dimajolkin/sms-telegram/docs/hardware/enclosure-bottom-iso.png

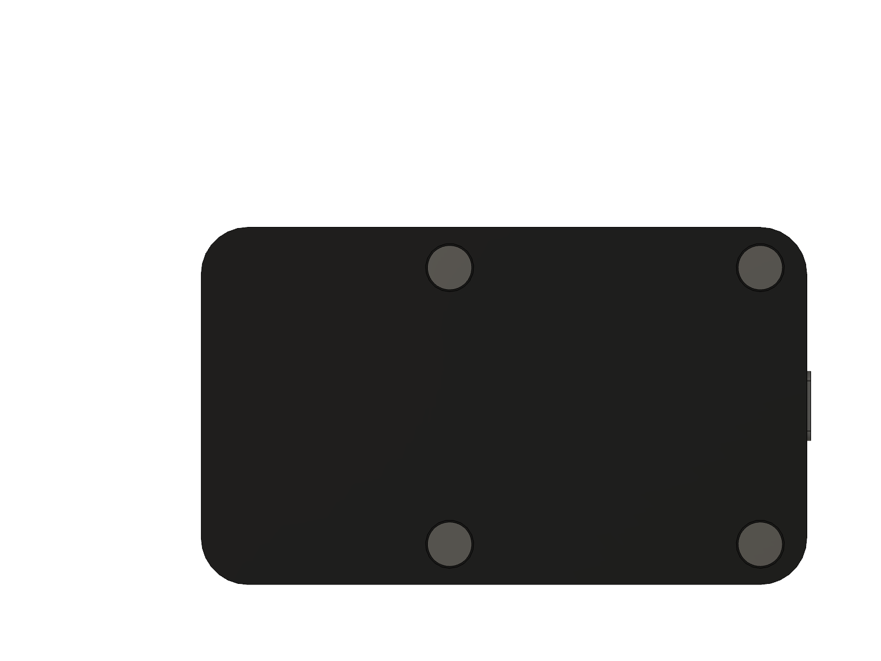
docs/hardware/enclosure-bottom-iso.png
