dimajolkin/sms-telegram/docs/hardware/enclosure-cover-fixtures.png

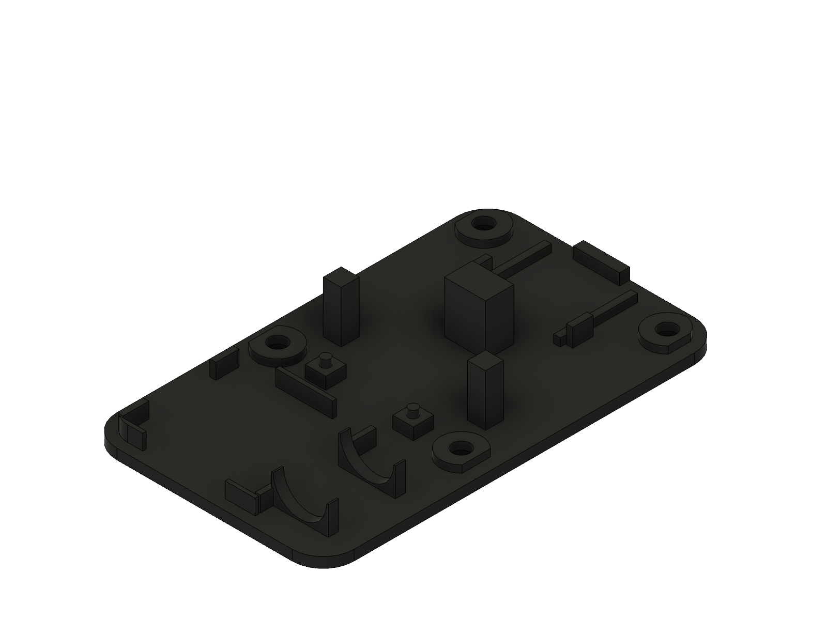
docs/hardware/enclosure-cover-fixtures.png
