dimajolkin/sms-telegram/docs/hardware/enclosure-front.png

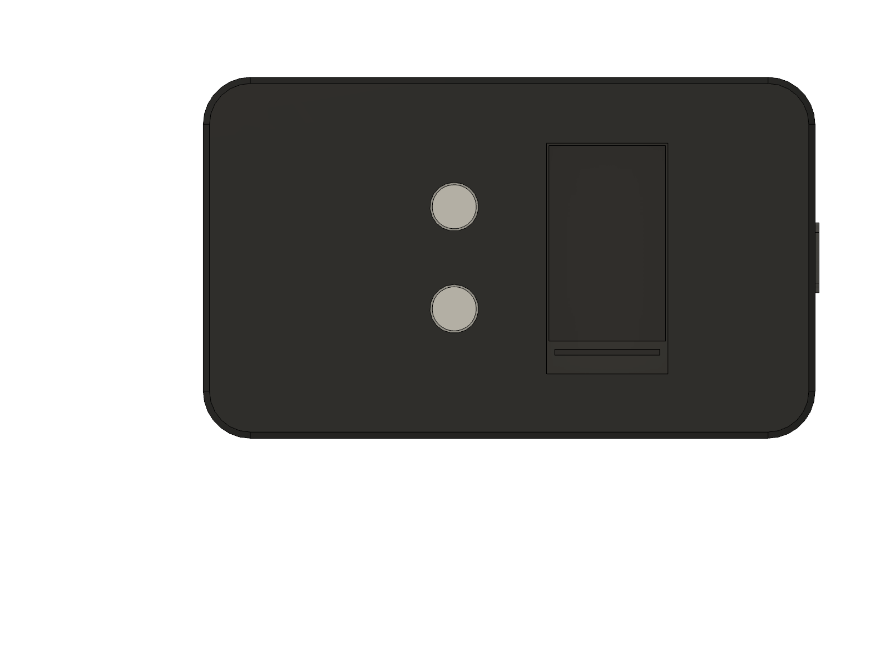
docs/hardware/enclosure-front.png
