dimajolkin/sms-telegram/docs/hardware/enclosure-usb-end.png

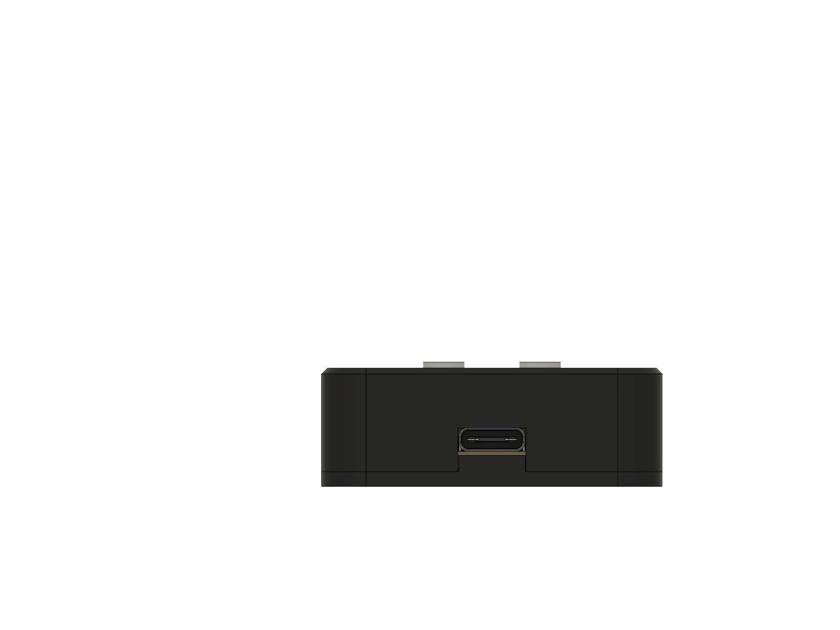
docs/hardware/enclosure-usb-end.png
