dimajolkin/sms-telegram/docs/sim800l-power-switch.png

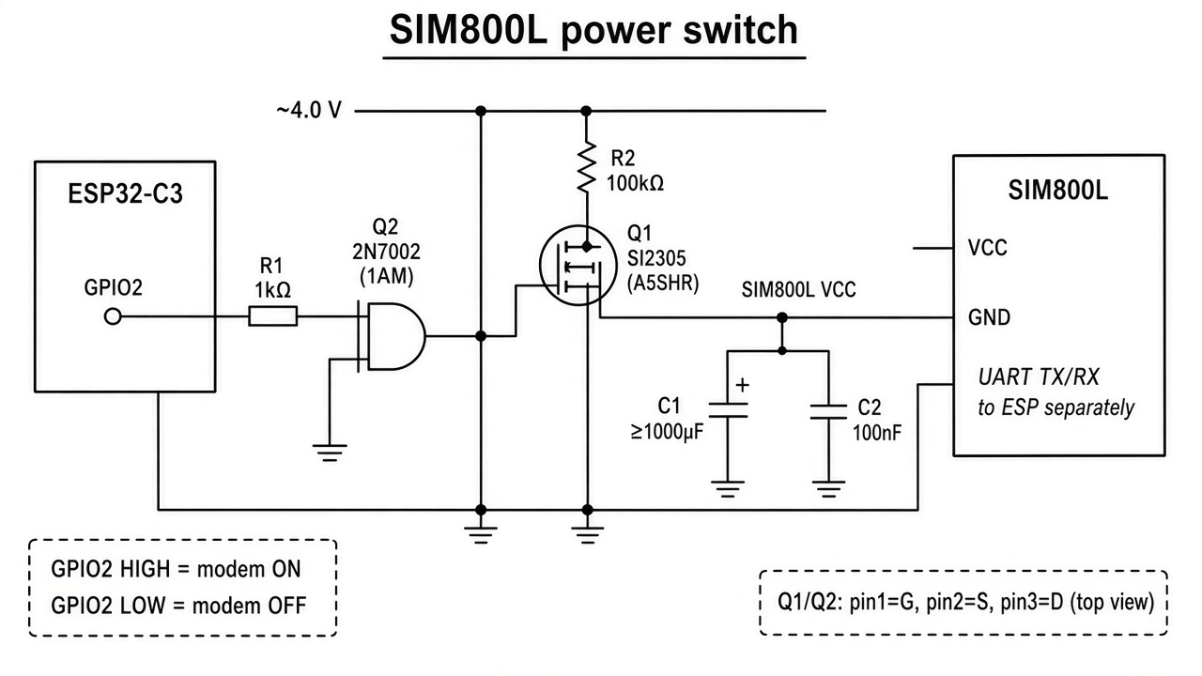
docs/sim800l-power-switch.png
